eositis/MegaFlash/docs/FujiNet-network-stack-on-MegaFlash.md

# Could FujiNet’s SmartPort-Based Network Stack Be Added to MegaFlash?

Short answer: **not as a direct drop-in**, but **yes in principle** by reusing the **design and protocol ideas** and reimplementing them on MegaFlash’s hardware and software stack.

---

## 1. How each project does “SmartPort” and network

### 1.1 FujiNet (Apple II)

- **Bus**: **IWM** (Intelligent Ware Manager). The Apple II talks to FujiNet over IWM: specific pins, packet encoding, and command set (status, status DIB, open, close, read, write, control).
- **Host**: **ESP32**. C++, full WiFi/TCP stack, `NetworkProtocol` (HTTP, TNFS, etc.), `ProtocolParser`, URL parsing.
- **Network device**: `iwmNetwork` in `lib/device/iwm/network.cpp`:
  - **Block-like**: Status (0x00), Status DIB (0x03) with `create_dib_reply_packet()` (same 25-byte DIB idea: status, block size, name, type, subtype, version).
  - **Channel/stream**: Open(URL), Close, Read channel, Write channel, and special status (e.g. FUJICMD_GETCWD, FUJICMD_READ, FUJICMD_STATUS). Uses `NetworkProtocol::open()`, `read()`, `write()`, URL → protocol (HTTP, TNFS, etc.).
- **DIB**: Same logical layout as ProDOS/SmartPort (e.g. type/subtype for “network”: `SP_TYPE_BYTE_FUJINET_NETWORK`, `SP_SUBTYPE_BYTE_FUJINET_NETWORK`).

So FujiNet’s “SmartPort-based network” = **IWM bus** + **SmartPort-style status/DIB** + **channel open/read/write** + **network protocol layer** on the ESP32.

### 1.2 MegaFlash

- **Bus**: **MegaFlash slot interface** (C0x registers: command, param, data). **Not IWM.** The Apple II runs 6502 assembly (`firmware/smartport.s`) that implements the **ProDOS block device** and **SmartPort** command set: Status, GetUnitStatus, GetDIB, ReadBlock, WriteBlock. That code calls into the slot ROM, which ultimately talks to the **Pico** via C0x (e.g. `CMD_GETDIB`, `CMD_READBLOCK`, `CMD_WRITEBLOCK`).
- **Host**: **Pico (RP2040/RP2350)**. C (no C++ network stack). Implements **block storage** only: flash, RAM disk, ROM disk. No URL, no HTTP/TNFS, no “open connection” semantics.
- **DIB**: Same 25-byte layout as FujiNet (`mediaaccess.h` `dib_t`: devicestatus, block size, id string, devicetype, subtype, firmware version). Device types: 0x00 RAM, 0x02 hard disk, 0x04 ROM disk. No “network” type yet.

So MegaFlash’s “SmartPort” = **same logical ProDOS/SmartPort protocol** (Status, GetUnitStatus, GetDIB, ReadBlock, WriteBlock) over **MegaFlash’s own transport** (C0x + command/param/data), and **only block devices** today.

---

## 2. Main incompatibilities (why not a direct port)

| Aspect | FujiNet | MegaFlash |
|---|---|---|
| **Hardware bus** | IWM (pins, timing, packet format) | C0x slot (command/param/data registers) |
| **MCU** | ESP32 | Pico (RP2040/RP2350) |
| **Language / stack** | C++, WiFi/TCP, NetworkProtocol, ProtocolParser | C, no network protocol layer |
| **Device model** | Block + **channel** (open URL, read/write stream) | Block only (ReadBlock, WriteBlock) |
| **Transport** | IWM packets, `iwm_send_packet()` | MegaFlash commands (CMD_*), param/data buffers |

So you **cannot** “run FujiNet firmware” on MegaFlash: different bus, different MCU, different transport. The FujiNet **network stack** (protocols, URL parsing, open/read/write) is tied to IWM and ESP32.

---

## 3. What *is* compatible (where “adding FujiNet-style network” makes sense)

- **Protocol semantics**: Both use the same **SmartPort/ProDOS device model**: Status, DIB (25-byte), and for storage ReadBlock/WriteBlock. FujiNet adds **channel** operations (open/read/write) for the N: device; MegaFlash could add the same **logical** operations (open URL, read/write stream) over its own transport.
- **DIB layout**: MegaFlash already has the same 25-byte DIB (`dib_t`). You could add a **network device type** (e.g. type/subtype for “network”, like FujiNet) and one or more “network units” that report a DIB and respond to **new** commands (open URL, read channel, write channel) instead of ReadBlock/WriteBlock.
- **Apple II side**: MegaFlash’s driver is in 6502 asm and talks to the Pico via existing CMD_* and param/data. To support an N: device you’d either:
  - Extend the **existing** SmartPort/ProDOS driver to recognize a “network” unit and send new commands (open, read channel, write channel), or
  - Add a **separate** driver (or slot) that only does network and uses the same C0x command/param/data protocol with new command bytes.

So the **compatibility** is at the **protocol and DIB level**, not at the bus or firmware binary level.

---

## 4. What would be required to add a FujiNet-like network stack to MegaFlash

### 4.1 On the Apple II side (MegaFlash firmware / driver)

- **New “network” unit type** in the SmartPort/ProDOS world:
  - Status and **GetDIB** for the network unit(s), with a DIB that identifies the device as network (type/subtype like FujiNet).
  - **New operations**: e.g. “open” (URL or path in param buffer), “read channel”, “write channel”, “close”, “status” (channel status). These would be invoked like existing SmartPort calls but dispatch to new command codes (e.g. `CMD_NET_OPEN`, `CMD_NET_READ`, `CMD_NET_WRITE`, `CMD_NET_CLOSE`, `CMD_NET_STATUS`) and use param/data buffers for URL and payload.
- **Driver**: Either extend `smartport.s` (and any ProDOS entry points) to handle the network unit and these new operations, or provide a separate N: driver that uses the same C0x interface.

### 4.2 On the Pico side (MegaFlash C code)

- **New commands** in `cmdhandler.c`: e.g. `CMD_NET_OPEN`, `CMD_NET_READ`, `CMD_NET_WRITE`, `CMD_NET_CLOSE`, `CMD_NET_STATUS`, and possibly `CMD_GETDIB` for the network unit returning a network DIB.
- **Network stack** on Pico:
  - **WiFi**: Pico W has WiFi (CYW43439). Use Pico SDK / lwIP (or similar) for TCP/UDP.
  - **URL parsing**: Parse device spec / URL from param buffer (e.g. `N:HTTP://HOST:PORT/PATH`) to decide protocol and target. This is the same **idea** as FujiNet’s `PeoplesUrlParser` and `parse_and_instantiate_protocol()`.
  - **Protocol layer**: Implement at least one protocol (e.g. HTTP GET, or TNFS) with **open** (connect, send request or open session), **read** (receive bytes into data buffer), **write** (send bytes from data buffer), **close**, **status**. This mirrors FujiNet’s `NetworkProtocol` and how `iwmNetwork` uses it.
- **Buffers**: Reuse or extend the existing param/data buffers for URL (param) and channel I/O (data). Optionally add a small “special” or status buffer if needed for channel status (e.g. bytes available, error code).

### 4.3 Reusing FujiNet code vs reimplementing

- **FujiNet’s C++ and ESP32**: The network protocol code (HTTP, TNFS, TCP, etc.) is C++, uses `std::string`, and ESP32 APIs. To run it on Pico you’d have to:
  - Port the **protocol logic** (and possibly a subset of `NetworkProtocol` / `ProtocolParser`) to Pico (C or C++ with Pico SDK).
  - Replace ESP32 WiFi/TCP with Pico/lwIP (or equivalent). That’s a non-trivial port but the **design** (URL → protocol, open/read/write/close) is directly reusable.
- **Protocol semantics**: FujiNet’s URL format, open modes, and channel read/write behavior can be **reimplemented** in C on the Pico so that existing Apple II software that expects “N: device” (e.g. fujinet-lib with unit-id) could work with MegaFlash’s N: device if the same command/status/DIB semantics are preserved.

So: you don’t “add the FujiNet binary”; you **add a network device to MegaFlash** that speaks the same **logical** SmartPort/ProDOS network protocol (DIB, status, open/read/write channel), implemented on the Pico, optionally inspired or adapted from FujiNet’s protocol layer.

---

## 5. Summary

| Question | Answer |
|---|---|
| **Same bus?** | No. FujiNet = IWM, MegaFlash = C0x. No shared hardware transport. |
| **Same firmware?** | No. Different MCU (ESP32 vs Pico), different bus, different APIs. |
| **Same protocol idea?** | Yes. Both use SmartPort-style Status/DIB and block or channel semantics. DIB layout (25 bytes) is already the same on MegaFlash. |
| **Can FujiNet’s *network stack* be “added” to MegaFlash?** | **Conceptually yes**: add a **network unit** to MegaFlash that exposes N: with open/read/write/close and a DIB, and implement on the Pico a **small network stack** (WiFi, URL parsing, at least one protocol like HTTP or TNFS). |
| **Practical approach** | (1) Define new MegaFlash commands and param/data usage for “network” (open URL, read channel, write channel, close, status). (2) Extend or add Apple II driver to call these. (3) On Pico, implement URL parsing and one or more protocols (e.g. HTTP); optionally port or reimplement logic from FujiNet’s `lib/network-protocol` and `lib/device/iwm/network.cpp` in C/C++ for Pico. |

So: **FujiNet’s SmartPort-based network stack cannot be “plugged in” to MegaFlash as-is**, but the **design and protocol** can be reused so that MegaFlash gains a compatible N: device with a Pico-based network implementation.

---

## 6. Could an existing FujiNet network application work with MegaFlash?

**Short answer: yes**, for the same **application logic** (open N:, read, write, close), **provided** the Pico implements the FujiNet network design and protocol and the Apple II uses an **N: driver that talks to MegaFlash** (C0x) instead of FujiNet (IWM). The application does not talk to the bus directly; it goes through ProDOS or a library, so it can work with either hardware as long as the driver and device behavior match.

### How an application talks to N:

- The **application** (e.g. BASIC, C, or assembly) does things like: open `N1:HTTP://example.com/`, read bytes, write bytes, close. It uses:
  - **ProDOS MLI** (e.g. open by path, read, write), or  
  - A **library** such as **fujinet-lib**, which wraps the N: device behind an API (open, read, write, status).
- In both cases, it is the **driver** (or library backend) that actually talks to the hardware: on FujiNet that’s IWM; on MegaFlash that would be C0x (command/param/data).

So the application only sees “N: device” with open/read/write/close semantics. It does **not** care whether the bytes go over IWM or C0x.

### What has to match for “existing FujiNet app” to work

| Layer | FujiNet | MegaFlash (with Pico updated) |
|---|---|---|
| **Application** | Same: OPEN N:…, READ, WRITE, CLOSE | Same: no change to app source or behavior. |
| **ProDOS / library API** | Same: N: device, same calls | Same: N: device, same calls. |
| **Driver / library backend** | Talks **IWM** to FujiNet | Must talk **C0x** to MegaFlash (different driver or library build). |
| **Device behavior (Pico)** | URL format, open/read/write/close, status, DIB, error codes | Must match FujiNet’s **protocol semantics** (URL format, open modes, read/write/close, status, DIB, errors). |

So:

1. **Pico** implements the same **protocol** as FujiNet’s N: device (URL format, open/read/write/close/status, DIB, and error behavior).
2. **Apple II** runs an **N: driver** (and/or library) that presents the same ProDOS/N: interface to the application but sends **C0x commands** (e.g. `CMD_NET_OPEN`, `CMD_NET_READ`, …) to MegaFlash instead of IWM to FujiNet.

Then the **same application** (same OPEN, READ, WRITE, CLOSE usage) works with MegaFlash. You are not running the FujiNet IWM driver; you are running a MegaFlash N: driver that is **protocol-compatible** with what the application expects.

### Caveats

- **Same binary?** If the app is compiled and linked against a library that talks **only** to FujiNet/IWM, that **binary** will not talk to MegaFlash. You need either:
  - An app that uses only ProDOS (and whatever N: driver is active), and you make the **active** N: driver the MegaFlash one, or  
  - A build of the library (or equivalent API) that uses the MegaFlash/C0x backend instead of IWM. Then the same **source** works; the **binary** may differ (different driver/library linked).
- **Protocol fidelity:** The Pico must implement the same URL semantics, open modes, status codes, and DIB so that existing apps and drivers that were written for FujiNet’s N: device get the behavior they expect.

**Bottom line:** If the Pico is updated with the FujiNet network design and protocol, an **existing FujiNet network application** (same program logic, same N: usage) **can** work with MegaFlash, using a **MegaFlash N: driver** (C0x) on the Apple II and **no** change to the application, as long as the protocol and device behavior match what that application expects.

---

## 7. Contiki and MegaFlash: would it need a driver change?

### Two different “Contiki” setups

1. **Contiki OS + Uthernet II (a2retrosystems / AppleWin)**  
   Full Contiki OS with a **W5100 driver** (`w5100.eth`) talking to the W5100 at C0x. That setup **would** need a driver change for MegaFlash (new driver or W5100 emulation), as in the paragraph below.

2. **FujiNet’s Contiki webbrowser** ([fujinet-contiki-webbrowser](https://github.com/FujiNetWIFI/fujinet-contiki-webbrowser))  
   This is the **canonical web browsing application** for Apple II (and Atari) on FujiNet. It does **not** use the W5100. It uses **FujiNet’s N: device** via **fujinet-lib**:
   - In `webclient.c`, the device is set to `"N:"` and all I/O goes through `network_open()`, `network_read()`, `network_close()`, `network_status()`, and `network_http_*()`.
   - The build pulls in **fujinet-lib** (e.g. v4.5.2) automatically; that library implements the `network_*` API and talks to the N: device (on FujiNet, over IWM).

So for **fujinet-contiki-webbrowser** specifically:

- **Application (contiki-webbrowser)**: **No change.** It already uses the N: device and the abstract `network_*` API; it does not touch IWM or C0x directly.
- **Driver / backend**: The hardware-facing code lives in **fujinet-lib**. On FujiNet, that library talks **IWM** to the N: device. For MegaFlash you need a **fujinet-lib** backend (or build) that talks **C0x** to MegaFlash’s N: implementation instead of IWM. So the **driver change** is in **fujinet-lib** (the layer that implements `network_*` against the hardware), not in the Contiki webbrowser source.

Once the Pico implements the FujiNet N: protocol and fujinet-lib has a MegaFlash/C0x backend, the **same** fujinet-contiki-webbrowser binary (or rebuild with the same source) can work with MegaFlash with **no application change**; only the library/driver that is linked or loaded needs to be the MegaFlash version.

### If using the other Contiki (OS + W5100)

The Contiki release that uses **Uthernet II** (e.g. from a2retrosystems, or with AppleWin’s Uthernet docs) uses a **W5100 driver** and expects raw W5100 register access at C0x. MegaFlash does not emulate the W5100, so that setup would still need either a new Contiki driver for MegaFlash’s N: protocol or MegaFlash emulating the W5100 (as in §7 table above).
