eositis/MegaFlash/pico/version.txt

Version 1.1.5 25-Aug-2025
Pico Firmware
- ADTPro VSDRIVE drivers are included in ROM Disk

Apple Firmware
- No changes (V1.0)

Version 1.1.4 18-Aug-2025
Pico Firmware
- Abort Erase Flash Disk if Apple is reset during the process
- Minor clean up of source code

Apple Firmware
- No changes (V1.0)

Version 1.1.3 15-Aug-2025
Pico Firmware
- Bug Fix: Last ProDOS block may contain incorrect data when transferring disk image to PC via XMODEM-1k
- Minor changes to device information output
- Improved SPI reliability by adding NOP to enable/disable_spi0() function
- Changed Mutex in flash.c to Recursive Mutex
- Added Mutex to ramdisk.c
- Show CPU and SPI speed on Device Information Screen

Apple Firmware
- No changes (V1.0)

Version 1.1.2 11-Aug-2025
Pico Firmware
- Set the drive strength of SPI output pins to 8mA
- Set the drive strength of Flash Chips to 75%
- Hide the clock during drive erase in Control Panel
- Bug Fix: System freeze during TFTP Download since V1.1

Apple Firmware
- No changes (V1.0)

Version 1.1.1 04-Aug-2025
Pico Firmware
- Recompiled with PICO SDK V2.2.0
- Minor changes to Control Panel UI Wording
- Changed Pico PIO output pins from pull-down to pull-up for Rev1.1 PCB

Apple Firmware
- No changes (V1.0)

Version 1.1 30-Jul-2025
Pico Firmware
- Bug Fix: Failed to download to RAM Disk via WIFI/TFP
- Bug Fix: Failed to detect of IO Error when TFTP Download
- Improved SPI Interface Reliability
- Option to erase the entire drive when formatting through the Control Panel
- Each drive can be individually enabled/disabled

Apple Firmware
- No changes (V1.0)

Version 1.0 21-Jul-2025
- First Public Release
- Supported Winbond W25Q02JV-DTR flash chip
