eositis/MegaFlash/pico/tftptxtask.cpp

#include "tftp.h"
#include "tftptask.h"
#include "tftptxtask.h"
#include "tftpstate.h"
#include "misc.h"
#include "mediaaccess.h"
#include "debug.h"
#include "defines.h"

extern "C" volatile tftp_state_t tftp_state;



// Constructor
// 
CTFTPTXTask::CTFTPTXTask(const uint32_t unitNum,const char* hostname,const char* filename,const bool enable1kBlockSize,const uint32_t tftpTimeout,
                         const uint32_t tftpMaxAttempt,const uint16_t tftpServerPort):
                         CTFTPTask(unitNum, hostname, filename,enable1kBlockSize,tftpTimeout,tftpMaxAttempt,tftpServerPort) {
  
  
  nextDataPacketBuf = new uint8_t[TXBUFFERSIZE];
  nextDataPacketLen = 0;
  
  OACKReceived = false;
  hasCompleted = false;
  serverTIDAccepted = false;
  blockSent = 0;
  tftpBlockSize = 512;
  blockCount = GetBlockCountForImageTransfer(unitNum); //Number of ProDOS blocks to be sent
  needToBuildNextPacket = false;
  DEBUG_PRINTF("Total blockCount=%d\n",blockCount);
}

//Destructor
//
CTFTPTXTask::~CTFTPTXTask() {
  delete []nextDataPacketBuf;
}


//Override Run()
//
void CTFTPTXTask::Run(const char* ssid, const char* wpakey){
  CTFTPTask::Run(ssid,wpakey);
}

//////////////////////////////////////////////////////////
//
// Event Start Handler
// Must run when the session starts (including NetworkPump path, which does not call Run()).
// tsize is required for Control Panel block line "N/M (pct%)" via TFTPFormatBlocksMessage.
//
void CTFTPTXTask::EvtStart() {
  const uint32_t tsize_bytes = blockCount * PRODOS_BLOCKSIZE;
  tftp_critical_section_enter_blocking();
  tftp_state.status = TFTPSTATUS_WIFICONNECTING;
  tftp_state.tsize = tsize_bytes;
  tftp_critical_section_exit();
  INFO_PRINTF("tftp_state.status = TFTPSTATUS_WIFICONNECTING, tsize bytes=%lu\n",
              (unsigned long)tsize_bytes);
  CTFTPTask::EvtStart();
}

//////////////////////////////////////////////////////////
//
// DNS Lookup Result Handler
//
void CTFTPTXTask::EvtDNSResult(const int dns_error, const ip_addr_t *ipaddr) {
  //Call base class implementation
  //Throw exception if hostname cannot be resolved.
  CTFTPTask::EvtDNSResult(dns_error,ipaddr);  
  
  //Hostname resolved.
  StartTransfer();
}

//////////////////////////////////////////////
// Start File Transfer by sending RRQ packet
//
void CTFTPTXTask::StartTransfer() {
  this->server_port = tftpServerPort; //Reset server_port TFTP Server listening port
  BuildWriteRequestPacket();
  if (enable1kBlockSize) {
    AddOption("blksize","1024");    
    AddOption("tsize", blockCount*PRODOS_BLOCKSIZE); //Tell server the file size
  }
  
  SendPacket();
  SetTimer(tftpTimeout);
  attempt = 1; //First Attempt
  current_tftpBlock = 0;  //Expecting to receive Ack Block #0 or OACK
  
  tftp_critical_section_enter_blocking();
  tftp_state.status = TFTPSTATUS_REQUEST;
  tftp_critical_section_exit();
  INFO_PRINTF("tftp_state.status = TFTPSTATUS_REQUEST\n");
  //The server will response with OACK if option negotiaion is supported or
  //it will response with ACK#0.
}

//////////////////////////////////////////////////////////
//
// UDP Received Handler
//
// Discard all invalid packet and let the timeout mechanism
// to retry.
//
void CTFTPTXTask::EvtUDPReceived(const uint8_t* payload,uint16_t payloadlen,ip_addr_t remote_addr,uint16_t remote_port){
  CTFTPTask::EvtUDPReceived(payload,payloadlen,remote_addr,remote_port);
  
  //validate the packet format
  if (payloadlen<4) {
    TRACE_PRINTF("Discard Packet: payloadlen<4\n");
    return;
  }

  //Check remote address
  if (!ip_addr_cmp(&server_addr,&remote_addr))  {
    TRACE_PRINTF("Discard Packet: remote_addr != server_addr\n");
    return;
  }
  
  //Check remote port
  //If server TID is not accepted, accept any remote port
  //Otherwise, accept remote_port == server_port only
  if (serverTIDAccepted && remote_port!=server_port) {
    TRACE_PRINTF("Discard Packet: Invalid remote port\n");
    return;
  }
  
  //check opcode should be 1-6
  const uint16_t opcode = payload[0]*256+payload[1];
  if (opcode==0 || opcode >=7) {
    TRACE_PRINTF("Discard Packet: Invalid TFTP OPCODE\n");
    return;
  }
  
  if (opcode == OP_OACK) ProcessOACKPacket(payload,payloadlen,remote_port);
  else if (opcode == OP_ACK) ProcessACKPacket(payload,payloadlen,remote_port);
  else if (opcode == OP_ERROR) ProcessErrorPacket(payload, payloadlen);
  //discard other opcode packets
    

}


////////////////////////////////////////////////////////////
// Process OACK Packet
//
// Parse the option-value pair from the payload
// then call the corresponding handler.
// Handler may throw E_NEEDRESTART. In this case,
// the data transfer is restarted.
#define E_NEEDRESTART (0)
void CTFTPTXTask::ProcessOACKPacket(const uint8_t* payload,uint16_t payloadlen,uint16_t remote_port) {
  //Aceept OACKPacket once and before first data packet
  if (OACKReceived || blockSent!=0) return;
  OACKReceived = true;
  DEBUG_PRINTF("OACK Received\n");
  
  //Accept remote_port (TID) 
  if (!serverTIDAccepted){
    server_port = remote_port;
    serverTIDAccepted = true;
    DEBUG_PRINTF("Setting server_port to %d\n",remote_port);    
  }
  
  //Parse and handle the options
  size_t currentPos=2;    //Option-Value pair starts at offset 2
  const char *option,*value;
  try {
    while(ParseOption(payload,payloadlen,&currentPos,&option,&value)) {
      DEBUG_PRINTF("option: %s=%s\n",option,value);
      if (0==strcmp(option,"blksize")) HandleOACK_blksize(value);
    }
  } catch(int e) {
    if (e==E_NEEDRESTART) {
      //
      // Restart the transfer
      //
      
      //Send Error Packet to terminate the previous connection
      BuildErrorPacket(TFTPERROR_DENIED_OPTIONS);   //error code #8
      SendPacket();
    
      //rebind UDP local interface so that local_port is changed and the server should recognise it as a new connection
      cyw43_arch_lwip_begin();
      udp_bind(this->pcb, IP4_ADDR_ANY, 0 /*random port*/); //Bind local IF
      cyw43_arch_lwip_end();  
      OACKReceived = false; 

      //Start again
      this->CancelTimer();      //Cancel any pending timer event
      this->StartTransfer();    //Send RRQ to start the transfer
      return;
    }
    assert(0); //unknown exception. should not happen
    return;
  }
  
  //Everything is ok.
  //Start data transfer by sending Data Packet
  SendDataPacket();
}

//////////////////////////////////////////////////////////
// Handle blksize option acknowledgement from server
//
// throw E_NEEDRESTART if the blksize is not 512 or 1024
//
void CTFTPTXTask::HandleOACK_blksize(const char* value) {
  bool is1024 = (0==strcmp(value,"1024"));
  bool is512 = (0==strcmp(value,"512"));
  
  //Only 512 and 1024 are acceptable
  if (is512 || is1024) {
    if (is1024) {
      INFO_PRINTF("Switching TFTP blockSize to 1024\n");
      tftpBlockSize=1024;
    }
  } else {
    //Unrecognised blksize. 
    //We don't expect it would happen since 1024 is a perfectly good
    //block size. 
    //Anyway, we try to restart the transfer without 1024 blksize option
    WARN_PRINTF("Unrecongised blksize. Restarting transfer without blksize option\n");
    enable1kBlockSize = false;  //Turn off 1024 blksize option
    throw E_NEEDRESTART;
  }
}


//////////////////////////////////////////////////////////
// Build and send Data packet
//
void CTFTPTXTask::SendDataPacket() {
  //First Data Packet?
  if (blockSent==0) {
    //Prepare first Data packet
    assert(current_tftpBlock==0);
    nextDataPacketLen = BuildDataPacket(nextDataPacketBuf,current_tftpBlock+1,blockSent);
    
    tftp_critical_section_enter_blocking();
    tftp_state.status = TFTPSTATUS_TRANSFER;
    tftp_critical_section_exit();
    INFO_PRINTF("tftp_state.status = TFTPSTATUS_TRANSFER\n");    
  }
  
  //Send Data Packet already in nextPacketBuf
  ++current_tftpBlock; //Advance to next TFTP block
  TRACE_PRINTF("Sending TFTP Data Packet Block=%d, len=%d\n",current_tftpBlock,nextDataPacketLen);
  SendPacket(nextDataPacketBuf,nextDataPacketLen);
  SetTimer(tftpTimeout);
  attempt = 1; //First Attempt  
  
  /**** Prepare next Data Packet while waiting Ack from server ****/
  
  //Copy nextPacket to txbuffer for Retry()
  //Also, update blockSent and hasCompleted
  memcpy(txbuffer,nextDataPacketBuf,nextDataPacketLen);
  txpacketlen = nextDataPacketLen;  
  uint32_t payloadlen = txpacketlen - 4; //4 bytes for Data Packet header
  blockSent += payloadlen/PRODOS_BLOCKSIZE;
  
  //Transfer Completed?
  if(payloadlen<tftpBlockSize) {
    hasCompleted = true;
  } else {
    // Defer building next packet to OnBeforeWait() so flash read runs outside UDP handler path (avoids stall/lockup after ~14 blocks)
    needToBuildNextPacket = true;
    nextBuildTftpBlock = current_tftpBlock + 1;
    nextBuildBlockSent = blockSent;
  }

  tftp_critical_section_enter_blocking();
  if (hasCompleted) tftp_state.status = TFTPSTATUS_COMPLETING;
  tftp_state.error = TFTPERROR_NOERR;
  tftp_state.blockTransferred = blockSent;
  tftp_critical_section_exit();
  if (hasCompleted) INFO_PRINTF("\ntftp_state.status = TFTPSTATUS_COMPLETING\n");
}

//////////////////////////////////////////////////////////
// Build Data Packet
// If tftpBlockSize, up to 2 ProDOS blocks is put into Data Packet.
//
// Input: destBuffer - Pointer to destination buffer
//        tftpBlock  - TFTP Block number of this packet
//        blockNum   - ProDOS block number of payload data
//
// Output: uint32_t - Length of Data Packet
//
uint32_t CTFTPTXTask::BuildDataPacket(uint8_t *destBuffer,uint16_t tftpBlockNum, uint32_t blockNum) {
  uint32_t packetLen = 4; //Length of header
  destBuffer[0] =0;
  destBuffer[1] = OP_DATA;
  destBuffer[3] = (uint8_t) tftpBlockNum;      //low byte
  destBuffer[2] = (uint8_t)(tftpBlockNum>>8);  //high byte
  
  //Special case blockNum == blockCount
  //All data has been sent. Send a Data packet without any payload
  //to end the transfer.
  assert(blockNum <= blockCount);
  if (blockNum == blockCount) {
    //Do nothing
  } else {
    //Put first block to payload
    assert(blockNum<=0xffff);
    uint error = ReadBlock(unitNum, blockNum++, destBuffer+4, NULL); //Read ProDOS block
    if (error!=MFERR_NONE) throw CTFTPTask::ERR_RWFAILED;   
    packetLen += PRODOS_BLOCKSIZE;
    
    //Put Second block to payload
    if (tftpBlockSize==1024) {
      if (blockNum<blockCount) {
        assert(blockNum<=0xffff);
        error = ReadBlock(unitNum, blockNum,destBuffer+4+512,NULL); //Read ProDOS block
        if (error!=MFERR_NONE) throw CTFTPTask::ERR_RWFAILED;           
        packetLen += PRODOS_BLOCKSIZE;
      }     
    }
  }
  
  assert(packetLen==4 || packetLen==516 || packetLen==1028);
  return packetLen;
}




//////////////////////////////////////////////////////////
// Build next data packet at start of event loop (deferred from SendDataPacket).
// Avoids doing flash/SPI (ReadBlock) inside UDP receive path, which can cause
// stall/lockup after several blocks (e.g. ~14) and require hard power-off.
//
void CTFTPTXTask::OnBeforeWait() {
  if (!needToBuildNextPacket || completed) return;
  nextDataPacketLen = BuildDataPacket(nextDataPacketBuf, nextBuildTftpBlock, nextBuildBlockSent);
  needToBuildNextPacket = false;
}

//////////////////////////////////////////////////////////
// Process ACK
// Accept remote_port if this is the first ACK Packet
//
void CTFTPTXTask::ProcessACKPacket(const uint8_t* payload,uint16_t payloadlen,uint16_t remote_port){
  uint16_t block = payload[2]*256+payload[3];
  TRACE_PRINTF("ACK Received block=%d\n",block);
  
  //First ACK Packet
  if (block==0 && blockSent==0) {
    //Accept remote_port (TID)
    if (!serverTIDAccepted){
      server_port = remote_port;
      serverTIDAccepted = true;
      DEBUG_PRINTF("Setting server_port to %d\n",remote_port);    
    }      
  }
  
  //Is it the ACK we are waiting for?
  if (block==current_tftpBlock) {
    //Proper Ack Received. Send next Data Packet unless hasCompleted is set
    if (hasCompleted) {
      this->Complete();
      tftp_critical_section_enter_blocking();
      tftp_state.status = TFTPSTATUS_COMPLETED;
      tftp_critical_section_exit();    
      INFO_PRINTF("tftp_state.status = TFTPSTATUS_COMPLETED\n");    
      INFO_PRINTF("TX Transfer Completed! Block Count = %d\n",blockSent);
    }
    else {
      SendDataPacket();
      return;
    }
  } else {
    //block number is not expected one.
    if (block==current_tftpBlock-1) {
      //If Ack of last Data Packet is received, it means the Data Block
      //is lost. Retry without any delay
      //Otherwise, Discard the packet.
      this->Retry();
      return;
    } else {
      TRACE_PRINTF("Discard Packet: Invalid Block Number\n");
      return;
    }
  }
}

//////////////////////////////////////////////////////////
// Timer timeout Handler
//
void CTFTPTXTask::EvtTimeout(uint32_t arg){
  this->Retry();
}

/////////////////////////////////////////////////////////////
// Retry Method
// See CTFTPTask::Retry()


//////////////////////////////////////////////////////////
// Process Error Packet
// See CTFTP::ProcessErrorPacket
