eositis/MegaFlash/pico/formatter.c

#include "pico/stdlib.h"
#include <string.h>
#include <ctype.h>
#include "defines.h"
#include "flash.h"
#include "mediaaccess.h"
#include "misc.h"
#include "rtc.h"

//There are 4 boot blocks in this source code. Currently, ProDOS 2.0.3 boot block is used

//ProDOS 2.5a8 Boot Block
static const uint8_t __attribute__((aligned(4))) bootBlockPD25a8[]={ //CRC32=A66A26B6
 0x01, 0x38, 0x78, 0xD8, 0xB0, 0x51, 0xA9, 0x0A,
 0x85, 0x86, 0xA2, 0x00, 0xA9, 0x01, 0x20, 0x79,
 0xF4, 0xB9, 0x00, 0xA0, 0x99, 0x00, 0x08, 0xB9,
 0x00, 0xA1, 0x99, 0x00, 0x09, 0xC8, 0xD0, 0xF1,
 0xA9, 0x4A, 0x8D, 0x90, 0x08, 0x8C, 0xFF, 0xC6,
 0x8C, 0xD0, 0xFF, 0x88, 0x8C, 0xDF, 0xFF, 0x4C,
 0x01, 0x08, 0x85, 0x45, 0xA9, 0xAE, 0x8D, 0xA8,
 0x05, 0xEE, 0x37, 0x08, 0x6C, 0x65, 0x08, 0x26,
 0x50, 0x52, 0x4F, 0x44, 0x4F, 0x53, 0x20, 0xC5,
 0xD2, 0xD2, 0xBD, 0x00, 0x0A, 0x01, 0x00, 0x6C,
 0x03, 0x96, 0xF3, 0x00, 0x04, 0x80, 0x04, 0xA8,
 0x8A, 0x4A, 0x4A, 0x4A, 0x4A, 0x09, 0xC0, 0x8D,
 0x66, 0x08, 0xC0, 0x07, 0xAC, 0xFF, 0xC6, 0xD0,
 0x10, 0xA0, 0x77, 0x8C, 0x3D, 0x08, 0xB0, 0x0D,
 0x48, 0xA9, 0x5B, 0x48, 0xE6, 0x3D, 0x60, 0x9D,
 0x09, 0x8C, 0x65, 0x08, 0x18, 0x86, 0x43, 0xA2,
 0x0D, 0xBD, 0x4A, 0x08, 0x95, 0x43, 0x86, 0x42,
 0xCA, 0xD0, 0xF6, 0x86, 0x40, 0xA0, 0x69, 0xB1,
 0x48, 0x99, 0x96, 0x0C, 0x88, 0x10, 0xF8, 0x8D,
 0x0C, 0xC0, 0xA2, 0x04, 0xA9, 0xA0, 0xA0, 0x77,
 0x91, 0x4C, 0x91, 0x4E, 0x88, 0x10, 0xF9, 0xE6,
 0x4D, 0xE6, 0x4F, 0xCA, 0xD0, 0xF0, 0xB0, 0x1F,
 0x20, 0x34, 0x08, 0xA2, 0xB1, 0x90, 0x18, 0x8E,
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

static const uint8_t block4[]={0x03,0x00, 0x05, 0x00};

static const uint8_t block5[]={0x04,0x00, 0x00, 0x00};


static const uint8_t bitMask[] = {
  0b11111111,
  0b01111111,
  0b00111111,
  0b00011111,
  0b00001111,
  0b00000111,
  0b00000011,
  0b00000001
};

//////////////////////////////////////////////////////
// Build Volume Bitmap Blocks
//
// Input: bitmapBlockNum - Bitmap Block Number (0-N)
//        blockBuffer    - Buffer to store generated data (512 Bytes)
//        blockCount     - Block Count of the volume
//
static void BuildVolumeBitmap(uint32_t bitmapBlockNum, uint8_t* blockBuffer, uint16_t blockCount) {
  const uint32_t BITSPERBLOCK = BLOCKSIZE * 8;
  const uint8_t UNUSEDFILL = 0x00;  //If the block is not a bitmap block, fill it with 0x00

  const uint32_t quotient = blockCount / BITSPERBLOCK;  //Number of complete Bitmap Block
  const uint32_t remainder = blockCount % BITSPERBLOCK;
  
  if (bitmapBlockNum < quotient) {
    //Whole Block is used as Bitmap Block
    memset(blockBuffer, 0xFF, BLOCKSIZE);
  }
  else if (bitmapBlockNum == quotient) {
    if (remainder == 0) {
      //Not a bitmap block
      memset(blockBuffer, UNUSEDFILL, BLOCKSIZE);
    } else {
      //Only a portion of block is used as volume bitmap
      memset(blockBuffer, 0x00, BLOCKSIZE);
      const uint32_t q = remainder / 8;
      const uint32_t r = remainder % 8;
      memset(blockBuffer, 0xff, q);
      blockBuffer[q] = ~bitMask[r];
    }
  }
  else {// bitmapBlockNum > quotient
    //The block is not a bitmap block
    memset(blockBuffer, UNUSEDFILL, BLOCKSIZE);
  }


  if (bitmapBlockNum == 0) {
    //First Volume Bitmap Block
    //Mark the blocks used by Boot Loader, Volume Directory and Bitmaps as used
    uint32_t numBlockUsed = 6 + quotient + (remainder!=0?1:0);  //7-21
    uint32_t index = 0;
    while (1) {
      if (numBlockUsed >= 8) {
        blockBuffer[index++] = 0x00; 
        numBlockUsed -= 8;
      }
      else {
        blockBuffer[index] = bitMask[numBlockUsed];
        break;
      }
    }
  }
}

//////////////////////////////////////////////////////
// Generate data for Block 0 - 21
//
// Input: blockNum    - Block Number (0-21)
//        blockBuffer - Buffer to store generated data (512 Bytes)
//        blockCount  - Block Count of the volume
//        volName     - Volume Name String
//        VolNameLen  - Volume Name Length
//
static void GenerateBlockData(uint32_t blockNum, uint8_t *blockBuffer,uint16_t blockCount,const char *volName,const uint32_t volNameLen) {
  assert(blockNum <= 21);
  assert(volNameLen<=15);
  
  const uint8_t *bootBlock = bootBlockPD203;
  
  //Block 0 - 1: Boot Loader
  if (blockNum == 0) {
    memcpy(blockBuffer, bootBlock, BLOCKSIZE);
    return;
  }

  if (blockNum == 1) {
    memcpy(blockBuffer, bootBlock+BLOCKSIZE, BLOCKSIZE);
    return;
  }

  //Block 2-5: Root Directory

  //Zero the buffer first
  if (blockNum >= 2 && blockNum <= 5) memset(blockBuffer, 0, BLOCKSIZE); 

  if (blockNum == 2) {
    memcpy(blockBuffer, block2, sizeof(block2));
    
    //Update Block Count
    blockBuffer[BLOCKCOUNTOFFSET]   = blockCount;
    blockBuffer[BLOCKCOUNTOFFSET+1] = blockCount>>8;
    
    //Update Volume Name
    if (volNameLen!=0) {
      strncpy(blockBuffer+VOLNAMEOFFSET, volName, 15);
      blockBuffer[VOLNAMELENOFFSET] = 0xf0 | (volNameLen&0x0f);
    }
    
    //Update Creation Date
    GetProdosTimestamp(blockBuffer+CREATETIONDATEOFFSET);
    
    return;
  }

  if (blockNum == 3) {
    memcpy(blockBuffer, block3, sizeof(block3));
    return;
  }

  if (blockNum == 4) {
    memcpy(blockBuffer, block4, sizeof(block4));
    return;
  }

  if (blockNum == 5) {
    memcpy(blockBuffer, block5, sizeof(block5));
    return;
  }

  //Block 6 - 21: Volume Bitmap
  if (blockNum >= 6 && blockNum <= 21) {
    BuildVolumeBitmap(blockNum - 6, blockBuffer, blockCount);
    return;
  }
}

//////////////////////////////////////////////////////
// Sanitize ProDOS Volume Name
// It makes sure the volume name is valid. i.e.
// 1) Maximum length = 15
// 2) Uppercase only
// 3) Only letters, digits and .(period)
// 4) Must begin with a letter.
//
// All invalid charactes are removed. If the result becomes
// an empty string, it sets the volume name to default.
//
// Input: volName - Volume Name string buffer
//
// Output: uint32_t - Length of the sanitized name
//
uint32_t SanitizeVolumeName(char* volName) {
  char c;
  
  //Remove all invalid characters
  uint j=0;
  for(uint i=0;i<FMT_VOLNAMEMAXLEN;++i) {
    c = volName[i];
    if (j==0 && !isalpha(c)) continue; //First char must be letter
    if (isalnum(c) || c=='.') {
      volName[j++] = toupper(c);
    }
    else if (c=='\0') break;
  }
  volName[j] ='\0';

  //If strlen == 0 or first char is not letter, set vol name to default
  if (strlen(volName)==0 || !isalpha(volName[0])) strcpy(volName,FMT_DEFAULTVOLNAME);
  
  return strlen(volName);
}

//////////////////////////////////////////////////////
// Format a unit
//
// Input: uintNum    - Unit Number
//        blockCount - Block Count of the unit
//        volName    - Volume Name
//        volNameLen - VOlume Name Length
//
// Output: success
//

bool FormatUnit(const uint32_t unitNum,const uint16_t blockCount,const char *volName,const uint32_t volNameLen) {
  uint8_t __attribute__((aligned(4))) blockBuffer[BLOCKSIZE];
  uint32_t blockAddress;
  bool success;
  uint error;
  
  if (blockCount<FMT_MINBLOCKCOUNT) return false; //Too small
  
  for(uint blockNum=0; blockNum<22; ++blockNum) {
    GenerateBlockData(blockNum, blockBuffer, blockCount, volName, volNameLen);
    error = WriteBlock(unitNum, blockNum, blockBuffer, NULL);
    if (error != MFERR_NONE) return false;
  }
  
  return true;
}
