eositis/MegaFlash/cpanel/config.h

#ifndef _CONFIG_H
#define _CONFIG_H
#include <stdint.h>
#include <stdbool.h>
#include "defines.h"

void InitConfig();
bool ValidateConfig(UserSettings_t* config);
void LoadConfig();
void SaveUserSettingsReboot();

#endif
