eositis/MegaFlash/cpanel/dialogs.c

#include <stdlib.h>
#include <string.h>
#include <conio.h>
#include <stdio.h>
#include <stdint.h>
#include <stdbool.h>
#include "defines.h"
#include "dialogs.h"
#include "ui-menu.h"
#include "ui-wnd.h"
#include "config.h"
#include "asm.h"
#include "textstrings.h"

// Defined in cpanel/main.c
extern UserSettings_t config;


//Working Variables
static uint8_t key;


/////////////////////////////////////////////////////////////
//
// Save Confirmation Dialog
//
/////////////////////////////////////////////////////////////
#define SC_XPOS 10
#define SC_YPOS 10
#define SC_WIDTH 20
#define SC_HEIGHT 6
static void DrawSaveConfirmWindow() {
  wnd_DrawWindow(SC_XPOS,SC_YPOS,SC_WIDTH,SC_HEIGHT,strConfirm,true,true);
}
/////////////////////////////////////////////
// Confirm to save the setting and rebot
// Return true if user select Yes
//
bool ShowSaveConfirmDialog() {
  DrawSaveConfirmWindow();
  cputs("Save and Reboot?");

  mnu_currentMenuItem=0;  //Default is Yes  
  do {
    key=DoMenu(yesnoMenuItem,2,2,2);
    if (key==KEY_ESC) return false;
  }while (key!=KEY_ENTER);
  
  if (mnu_currentMenuItem == 0) {
    DrawSaveConfirmWindow();
    cputs(strSaving);
  }

  //true if mnu_currentMenuItem==0
  //mnu_currentMenuItem is either 0 or 1
  //Inverting bit 0 is equivalent to mnu_currentMenuItem==0
  return mnu_currentMenuItem^0x01;
}



/////////////////////////////////////////////////////////////
//
// Erase All Settings Dialog
//
/////////////////////////////////////////////////////////////
#define ES_XPOS 5
#define ES_YPOS 9
#define ES_WIDTH 30
#define ES_HEIGHT 7

static void DrawEraseSettingsWindow() {
  wnd_DrawWindow(ES_XPOS,ES_YPOS,ES_WIDTH,ES_HEIGHT,strConfirm,true,true);
}

//Erase all settings from Pico Flash Memory
void ShowEraseSettingsDialog() {
  DrawEraseSettingsWindow();
  cputs("Reset all options to default\n\rand erase WIFI settings?");

  mnu_currentMenuItem=1;  //Default is No
  do {
    key=DoMenu(yesnoMenuItem,2,2,3);
    if (key==KEY_ESC) return;
  }while (key!=KEY_ENTER);
  
  if (mnu_currentMenuItem == 0) {
    DrawEraseSettingsWindow();    
    cputs(strErasing);
    
    EraseAllSettings(); 
    DriveMapping(false);  //EraseAllSettings() disable RAMDisk. Disable drive mapping to make sure we can access
                          //to all drives
    LoadConfig();   //Reload Config
    //Control Panel always enables ROM disk at startup (for access ordering),
    //but after a full reset the new default should be "ROM disk hidden"
    //unless explicitly enabled in the Drives Enable page.
    if (!(config.configbyte1 & ROMDISKFLAG)) {
      DisableRomdisk();
    }
    DisplayTime();  //Timezone may have changed. Update the clock
    
    cputs(strDone);  
    gotoxy(18,6);
    cputs(strOKAnyKey);
    cgetc();
  }
}


/////////////////////////////////////////////////////////////
//
// PicoW Needed Dialog
//
/////////////////////////////////////////////////////////////
void ShowPicoWNeededDialog() {
  wnd_DrawWindow(5,9,30,5,strError,true,true);
  cputs("Wifi requires PicoW Board.");
  gotoxy(18,4);
  cputs(strOKAnyKey);
  cgetc();
}
