eositis/MegaFlash/cpanel/asm.h

#ifndef _ASM_H
#define _ASM_H

#include <stdint.h>


//
// asm-megaflash.s
//
void __fastcall__ SendCommand();
bool __fastcall__ GetInfoString(uint8_t type);
uint8_t __fastcall__ GetUnitCount();
uint8_t __fastcall__ EraseDisk();
uint8_t __fastcall__ FormatDisk();
bool __fastcall__ GetVolInfo(uint8_t unitNum,void* pVolInfo);
uint8_t __fastcall__ TestWifi();
void __fastcall__ EraseAllSettings(); 
uint16_t __fastcall__ GetUnitBlockCount(uint8_t unitNum);
void __fastcall__ DriveMapping(bool enable);
void __fastcall__ DisplayTime();
void __fastcall__ ClearTime();
bool __fastcall__ SaveSetting(uint8_t cmd, uint8_t len, void* src);
bool __fastcall__ LoadSetting(uint8_t cmd, uint8_t len, void* dest);
void __fastcall__ PrintStringFromDataBuffer();
uint8_t __fastcall__ CopyStringToDataBuffer(void* src);
uint8_t __fastcall__ CopyStringFromDataBuffer(void* dest);
uint8_t __fastcall__ GetParam8Offset(uint8_t offset);
uint8_t  __fastcall__ GetParam8();
uint16_t __fastcall__ GetParam16();
uint8_t __fastcall__ StartTFTP(uint8_t flag,uint8_t dir,uint8_t unitNum);
void  __fastcall__ GetTFTPStatus(uint8_t pbMaxValue);
void __fastcall__ EnableRomdiskAtLast(void);  /* ROM disk at last SmartPort unit */
void __fastcall__ DisableRomdisk(void);       /* Hide ROM disk from SmartPort */
void __fastcall__ BootToRomdisk(void);        /* ROM disk first, then reboot (no return) */
void __fastcall__ Beep(void);                 /* Brief speaker beep (cc65 2.19 lacks apple2 beep) */
#define beep Beep

//
// asm-conio.s
//
void __fastcall__ cputchar_direct(char c);
void __fastcall__ fillchar_direct(char c,uint8_t count);
char __fastcall__ cgetchar(char cursor);
void __fastcall__ newline();
void __fastcall__ newline2();
void __fastcall__ newlinex(uint8_t x);
void __fastcall__ cursordown();
void __fastcall__ cursorup();
void __fastcall__ cursorupx(uint8_t xpos);
void __fastcall__ cursorupx_m1(uint8_t xpos);
void __fastcall__ cursorleft();
void __fastcall__ gotoxy00();
void __fastcall__ clreol();
void __fastcall__ set40();
void __fastcall__ set80();
void __fastcall__ setvid();

//
// asm.s
//
void __fastcall__ Reboot();
uint8_t __fastcall__ IsAppleIIcplus();
void __fastcall__ ToUppercase(char* s);
void __fastcall__ ZeroMemory(uint8_t len,void* dest);
bool __fastcall__ HasFPUSupport();
bool __fastcall__ ReadOpenAppleButton();
void __fastcall__ Delay(uint8_t n);

#endif
