eositis/MegaFlash/cpanel/textstrings.c

#define _TEXTSTRINGS_C
#include "textstrings.h"

const char strConfirm[] = "Confirm";
const char strError[] = "Error";
//const char strYes[] = "Yes";
//const char strNo[] = "No";
const char strOKAnyKey[]="OK:Any Key";
const char strAborted[] = "Aborted.";
const char strResult[] = "Result:";
const char strCurrent[] = "Current:";
const char strNew[] = "New:";
const char strRemote_[] = "Remote ";
const char strFilename[] = "Filename:";
const char strSaving[] = "Saving...";
const char strSave[] = "Save";
const char strrequired[] = "required";
const char stroptional[] = "optional";
const char strProDOS[] = "ProDOS";
const char strEmpty[] = "Empty";
const char strUnknown[] = "Unknown";
const char strFormatting[] = "Formatting...";
const char strErasing[] = "Erasing...";
const char strDone[] = "Done!";
const char str____OK[] = "    OK";
const char strFailed[] = "Failed";
const char strStarting[] = "Starting";
const char strTFTP_Download[] = "TFTP Download";
const char strTFTP_Upload[] = "TFTP Upload";
const char strServer[] = "Server:";
const char strStatus[] = "Status:";
const char strBlocks[] = "Blocks:";
const char strRetransmit[] = "Retransmit:";
const char strTime[] = "Time:";
const char strPressanykeyto_[] ="Press any key to ";
const char strcontinue[] = "continue";
const char strreboot[] = "reboot";
const char strOK_Enter[] = "OK:\315";
const char strCancelesc[] = "Cancel:esc";

const char strEditPrompt[] = "Cancel:esc   \310\323:delete     Next:\315";
char strDriveNumberPrompt[]  = "Drive Number (1- )? ";
const char strVolNameFormat[]   = " Name  = %s\n\r";
const char strVolSizeFormat[]   = " Size  = %u Blocks\n\r";
const char strEraseDrive[] = " Erase the drive = ";

const char* yesnoMenuItem[] = {
  "Yes",
  "No"
};
